Kshfiii/Esp32-Xiao-Cam-with-touch-screen/Assembly/Assembly_sideview_open.PNG

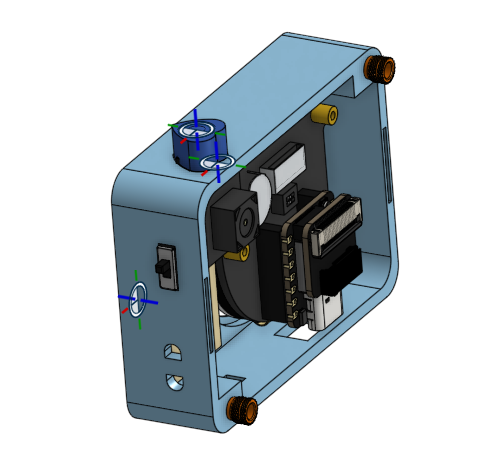
Assembly/Assembly_sideview_open.PNG
