Kshfiii/Esp32-Xiao-Cam-with-touch-screen/Assembly/Body_part1_front.PNG

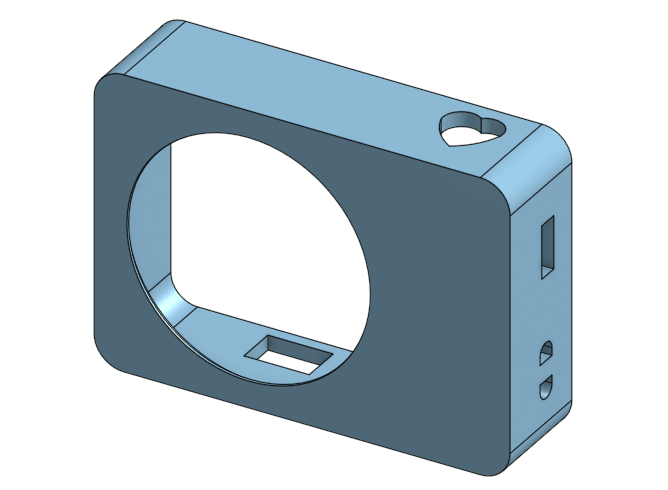
Assembly/Body_part1_front.PNG
